egeht/CWTrainer/hardware/CWTrainer.kicad_sch

## KiCad design hardware/CWTrainer.kicad_sch (2026-07-03)

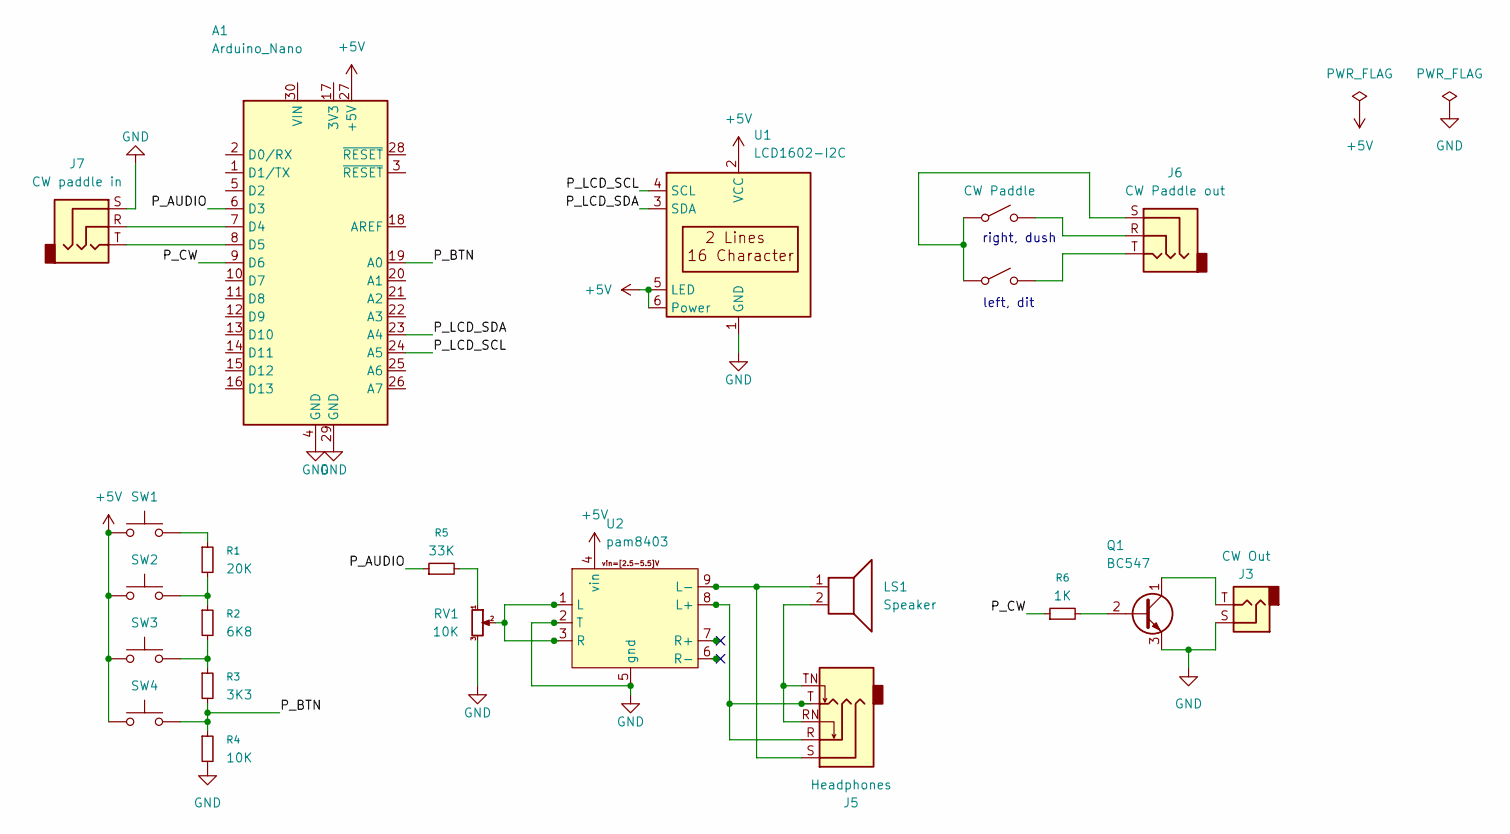
[picture p8: schematic CWTrainer.kicad_sch]

Parts:
A1: Arduino_Nano
J3: CW Out
J5: Headphones
J6: CW Paddle out
J7: CW paddle in
LS1: Speaker
Q1: BC547; TO-92_Inline
R1: 20K
R2: 6K8
R3: 3K3
R4: 10K
R5: 33K
R6: 1K
RV1: 10K
SW1, SW2, SW3, SW4: (no value)
SW5: CW Paddle
U1: LCD1602-I2C
U2: pam8403

Connections:
+5V: A1.27 (+5V), SW1.1, SW2.1, SW3.1, SW4.1, U1.2 (VCC), U1.5 (LED), U1.6 (Power), U2.4 (vin)
GND: A1.4 (GND), A1.29 (GND), J3.S, J7.S, Q1.3 (E), R4.2, RV1.3, U1.1 (GND), U2.2 (T), U2.5 (gnd)
unnamed: A1.7 (D4), J7.R
unnamed: A1.8 (D5), J7.T
unnamed: J3.T, Q1.1 (C)
unnamed: J5.R, J5.T, U2.8 (L+)
unnamed: J5.RN, J5.TN, LS1.2
unnamed: J5.S, LS1.1, U2.9 (L-)
unnamed: J6.R, SW5.2 (B)
unnamed: J6.S, SW5.1 (A), SW5.3 (A)
unnamed: J6.T, SW5.4 (B)
unnamed: Q1.2 (B), R6.2
unnamed: R1.1, SW1.2
unnamed: R1.2, R2.1, SW2.2
unnamed: R2.2, R3.1, SW3.2
unnamed: R5.2, RV1.1
unnamed: RV1.2, U2.1 (L), U2.3 (R)
P_AUDIO: A1.6 (D3), R5.1
P_BTN: A1.19 (A0), R3.2, R4.1, SW4.2
P_CW: A1.9 (D6), R6.1
P_LCD_SCL: A1.24 (A5), U1.4 (SCL)
P_LCD_SDA: A1.23 (A4), U1.3 (SDA)

Notes on the sheet:
left, dit
right, dush
